richardhawthorn/Clock1/images/pcb_back.png

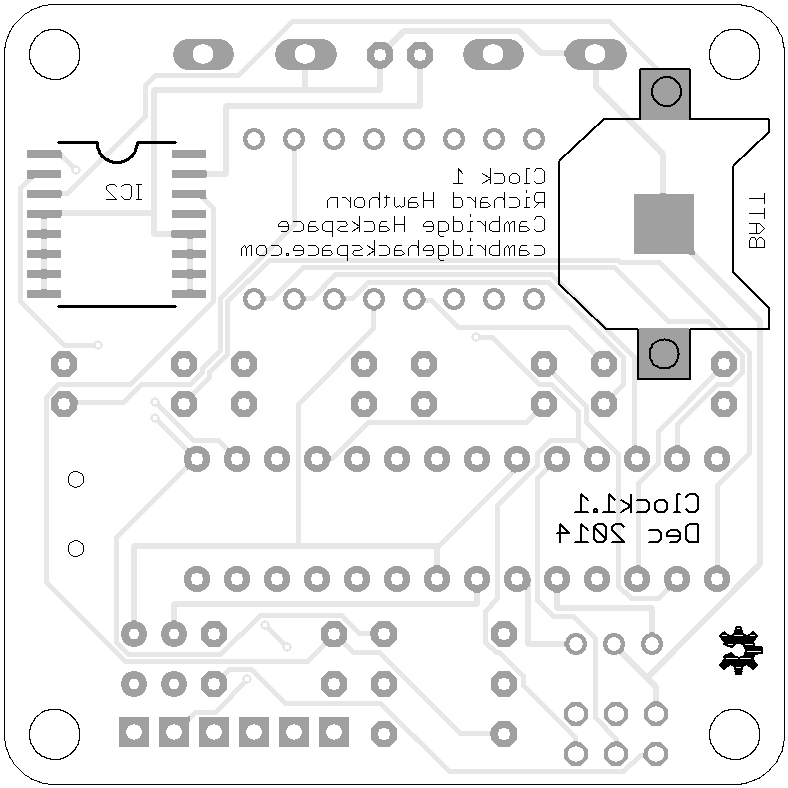
images/pcb_back.png
