richardhawthorn/Clock1/images/pcb_back_1.2.png

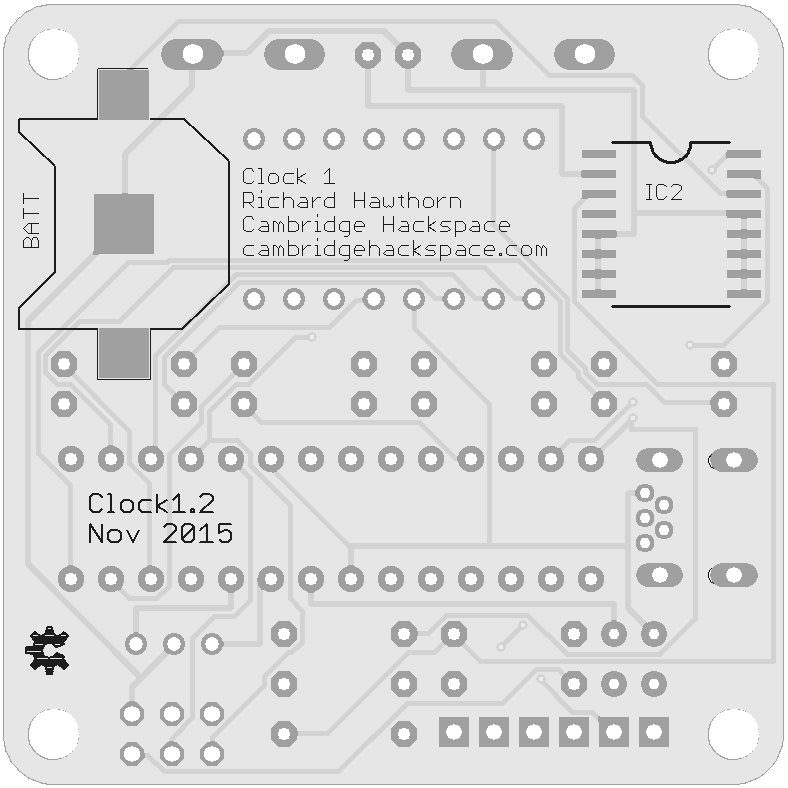
images/pcb_back_1.2.png
