richardhawthorn/Clock1/images/photo1.jpg

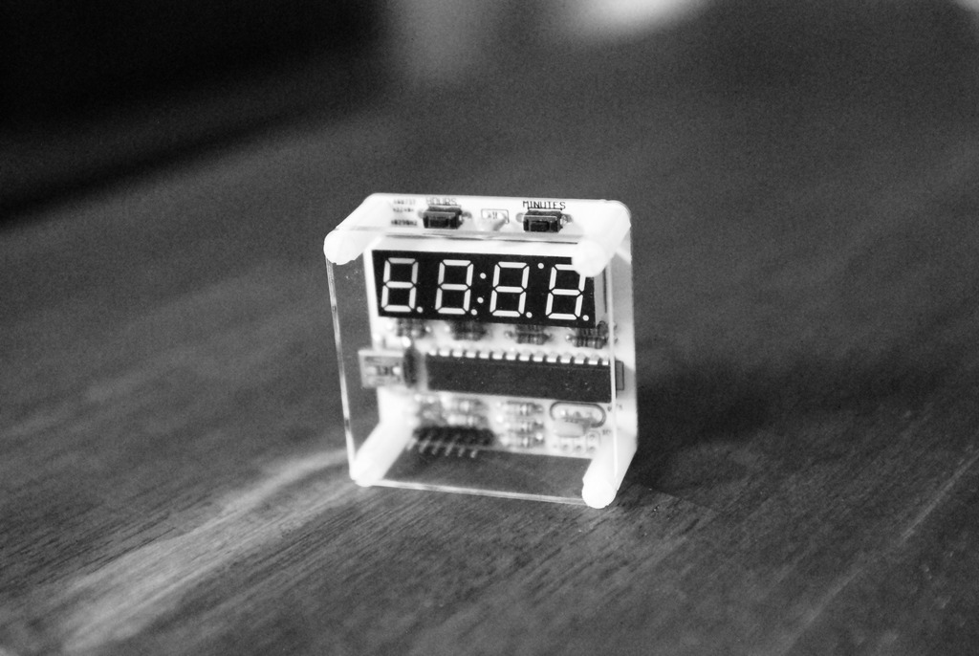
images/photo1.jpg
