richardhawthorn/Clock1/images/photo2.jpg

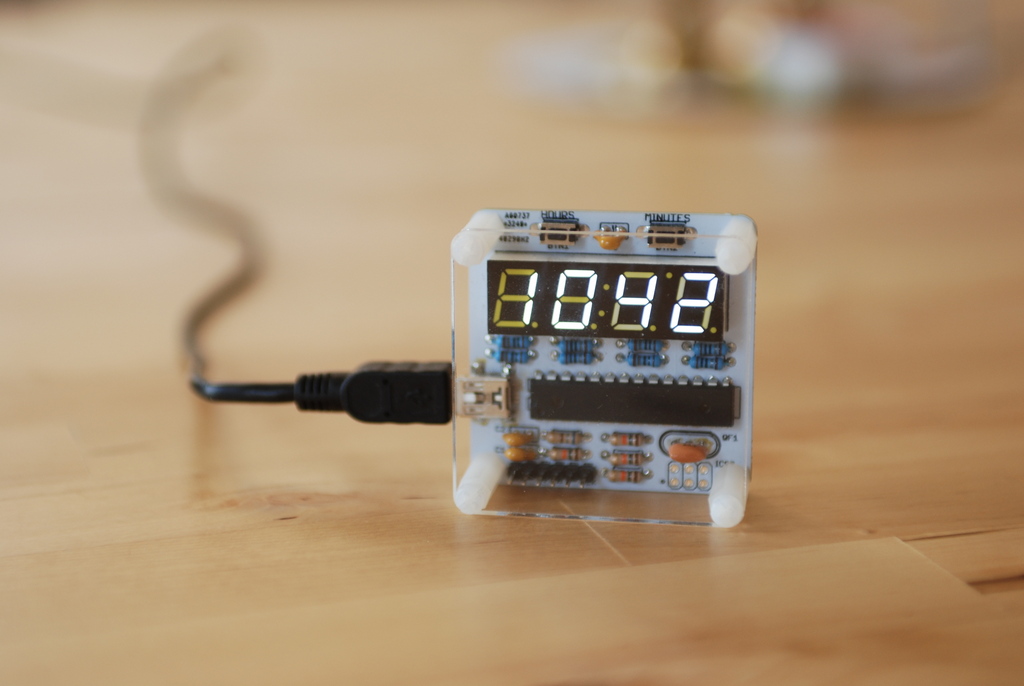
images/photo2.jpg
